zhangzw0170/Electronic_Load/Software/MCU_a9.1/Hardware/Component/OLED_Font.h

#ifndef __OLED_FONT_H
#define __OLED_FONT_H

// OLED 中文及特殊字模库，高 16 像素，宽 16 像素
const uint8_t SP_F16x16[][16] = {
	// 取模：阴码 列行式 逆向 C51格式
	
    // （空格）(0) 电(1) 子(2) 负(3) 载(4) 压(5) 流(6) 
	// 调(7) 整(8) 率(9) 设(10) 置(11) 
	// 恒(12) 输(13) 出(14) 中(15) 件(16) 
	// （左箭头）(17) （右箭头）(18)
	// （打勾）(19) （打叉）(20)
	// 开机（左上，上，右上，右，右下，下，左下，左）(21-28)
	// 正(29) 在(30) 
	// 张(31) 志(32) 文(33) 
	// 陈(34) 彦(35) 权(36)
	// 关(37) 于(38)
	// 菜(39) 单(40)
	// 已(41) 就(42) 绪(43)
	// 最(44) 近(45) 结(46) 果(47)
	// 测(48) 量(49)
	// 自(50) 动(51) 试(52)
	// 当(53) 前(54)
	// 默(55) 认(56)

	{0x00,0x00,0x00,0x00,0x00,0x00,0x00,0x00,0x00,0x00,0x00,0x00,0x00,0x00,0x00,0x00},
	{0x00,0x00,0x00,0x00,0x00,0x00,0x00,0x00,0x00,0x00,0x00,0x00,0x00,0x00,0x00,0x00},/* 空格 0 */

	{0x00,0x00,0xF8,0x88,0x88,0x88,0x88,0xFF,0x88,0x88,0x88,0x88,0xF8,0x00,0x00,0x00},
	{0x00,0x00,0x1F,0x08,0x08,0x08,0x08,0x7F,0x88,0x88,0x88,0x88,0x9F,0x80,0xF0,0x00},/*"电",1*/
	/* (16 X 16 , 宋体 )*/

	{0x80,0x82,0x82,0x82,0x82,0x82,0x82,0xE2,0xA2,0x92,0x8A,0x86,0x82,0x80,0x80,0x00},
	{0x00,0x00,0x00,0x00,0x00,0x40,0x80,0x7F,0x00,0x00,0x00,0x00,0x00,0x00,0x00,0x00},/*"子",2*/
	/* (16 X 16 , 宋体 )*/

	{0x00,0x20,0x10,0xE8,0x24,0x27,0x24,0xA4,0x24,0x34,0x2C,0xE0,0x00,0x00,0x00,0x00},
	{0x00,0x80,0x80,0x4F,0x40,0x20,0x18,0x07,0x10,0x10,0x20,0x4F,0x80,0x00,0x00,0x00},/*"负",3*/
	/* (16 X 16 , 宋体 )*/

	{0x90,0x94,0x94,0xF4,0x9F,0x94,0x94,0x94,0x10,0x10,0xFF,0x10,0x12,0xD4,0x10,0x00},
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
	
	0x00,0x00,0x00,0x00,0xFF,0x00,0x00,0x00,
	0x00,0x00,0x00,0x00,0xFF,0x00,0x00,0x00,//| 92
	
	0x00,0x02,0x02,0x7C,0x80,0x00,0x00,0x00,
	0x00,0x40,0x40,0x3F,0x00,0x00,0x00,0x00,//} 93
	
	0x00,0x06,0x01,0x01,0x02,0x02,0x04,0x04,
	0x00,0x00,0x00,0x00,0x00,0x00,0x00,0x00,//~ 94
};

#endif
